ItzShubhamDev/k90r/pcb/Keyboard.kicad_sch

## KiCad design pcb/Keyboard.kicad_sch (2025-08-02)

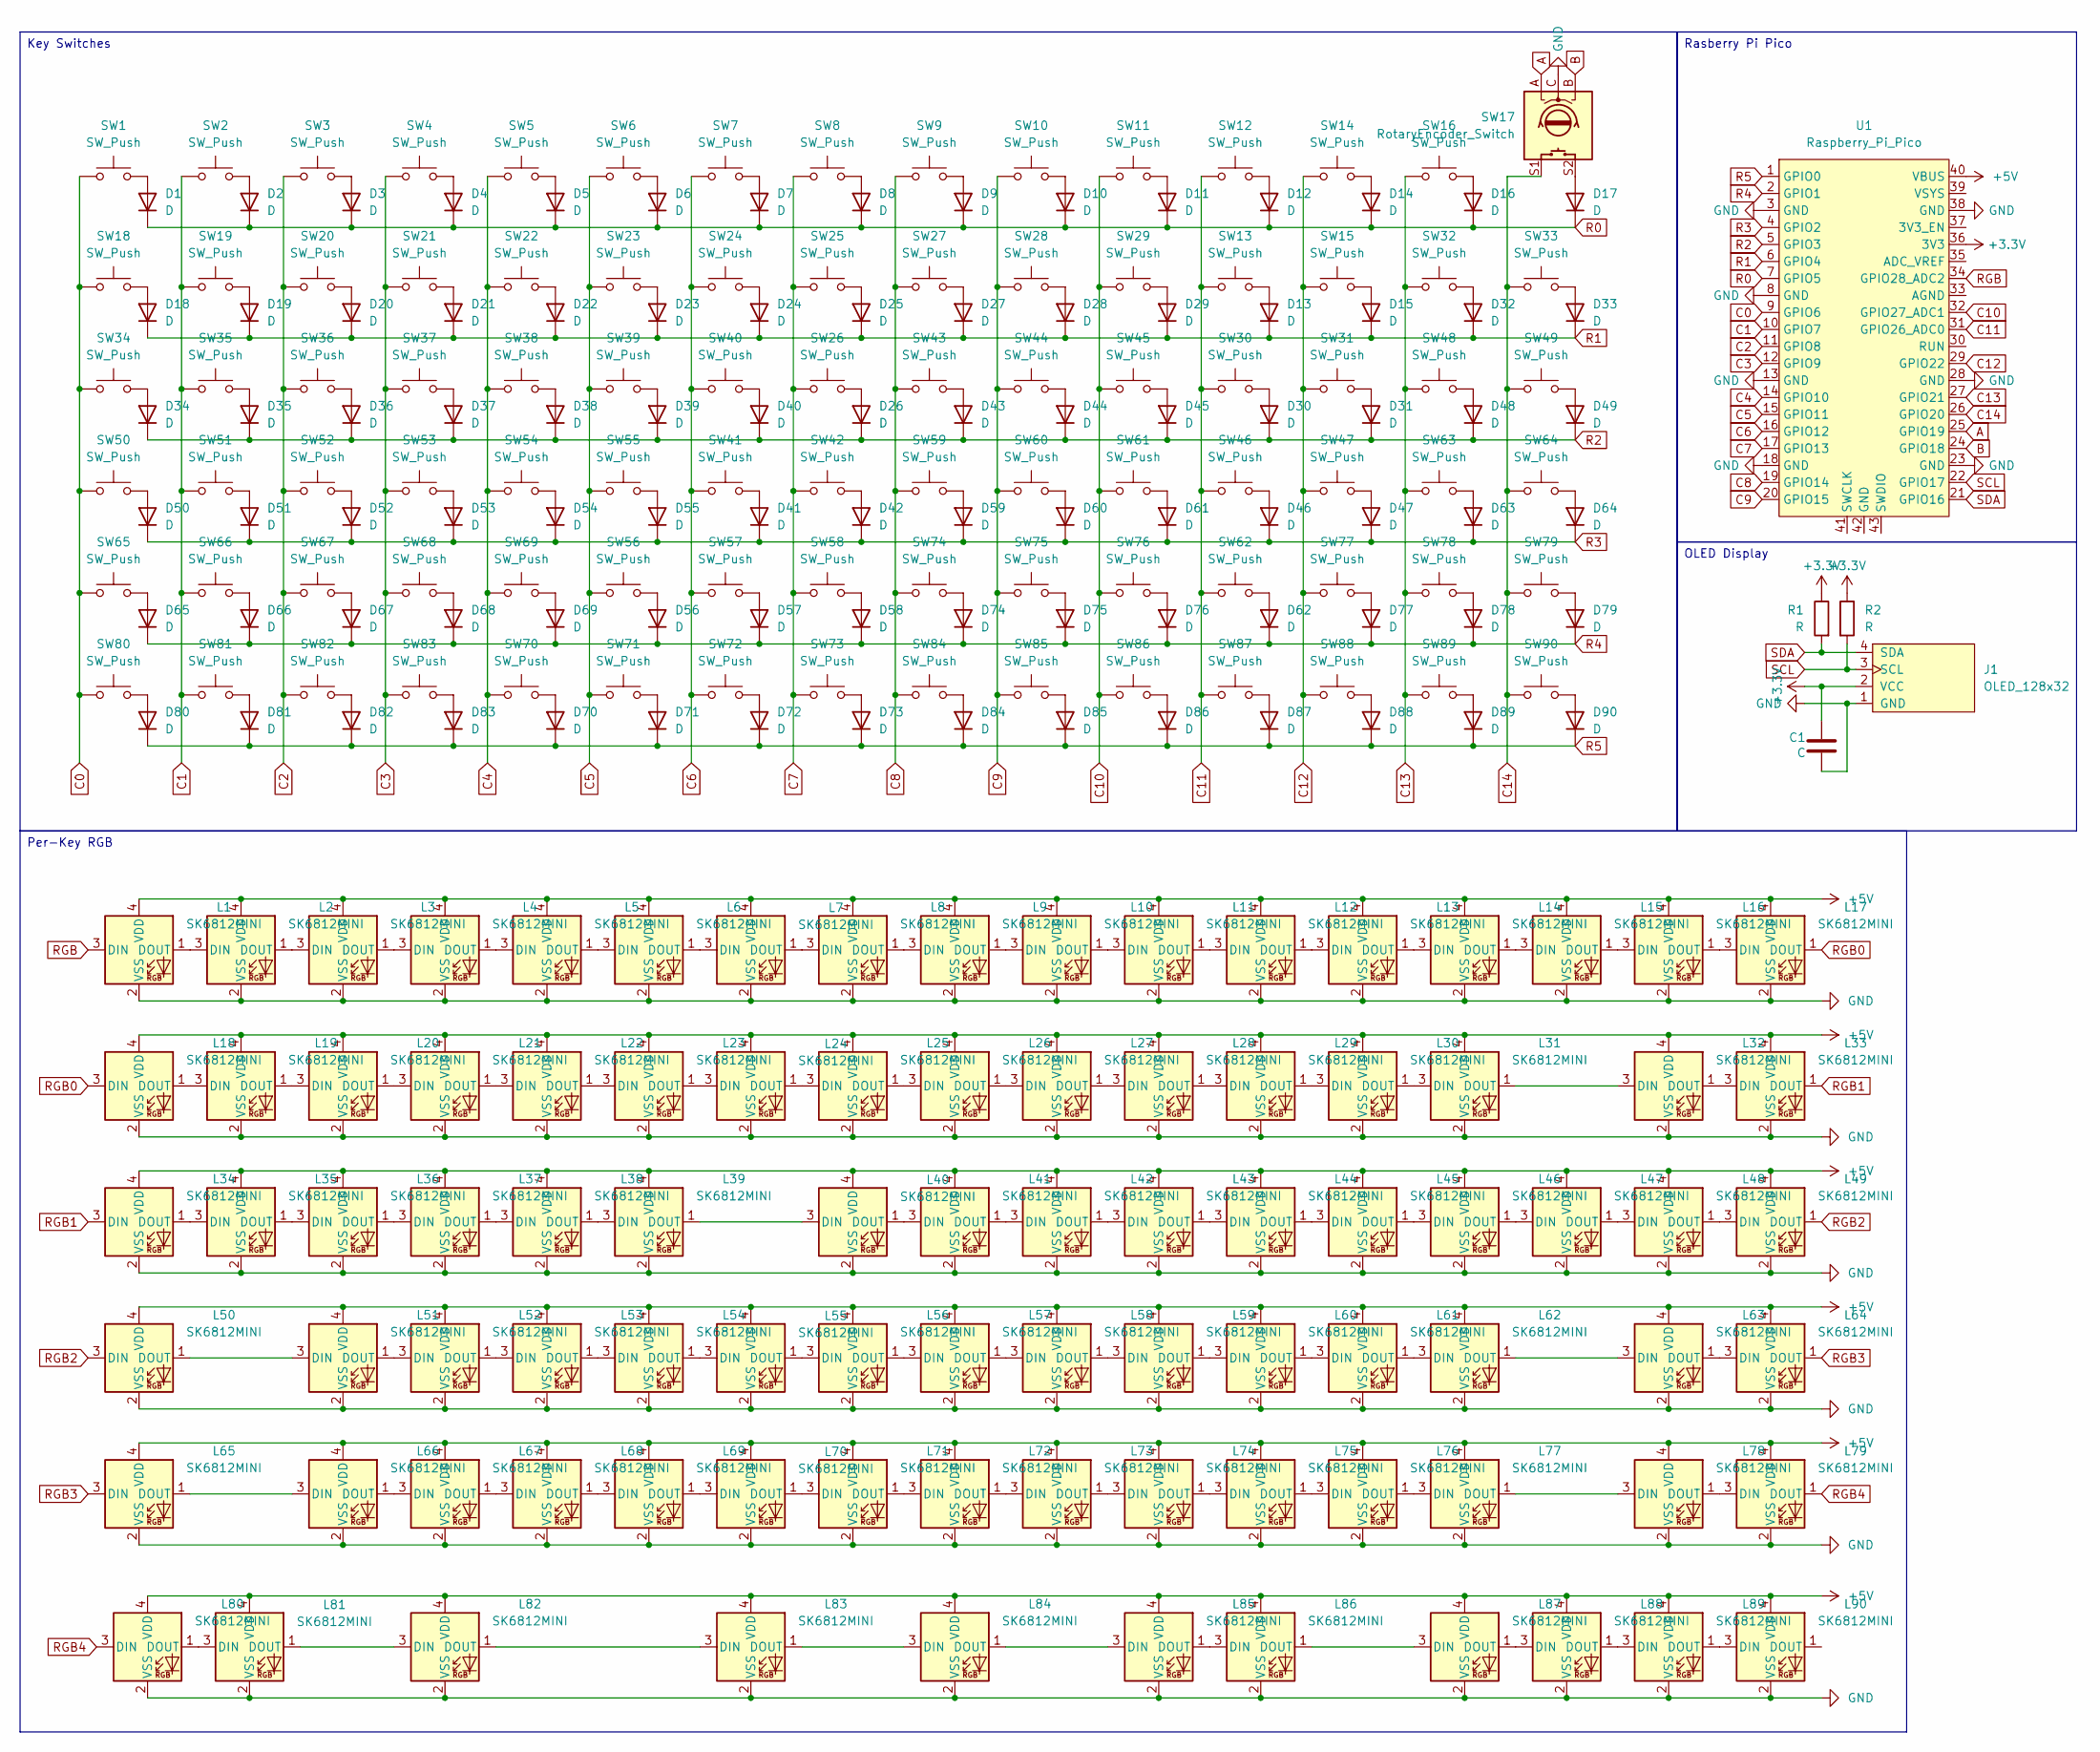
[picture p22: schematic Keyboard.kicad_sch]

Parts:
C1: C; C_Axial_L5.1mm_D3.1mm_P15.00mm_Horizontal
D1, D2, D3, D4, D5, D6, D7, D8, D9, D10, D11, D12, D13, D14, D15, D16, D17, D18, D19, D20, D21, D22, D23, D24, D25, D26, D27, D28, D29, D30, D31, D32, D33, D34, D35, D36, D37, D38, D39, D40, D41, D42, D43, D44, D45, D46, D47, D48, D49, D50, D51, D52, D53, D54, D55, D56, D57, D58, D59, D60, D61, D62, D63, D64, D65, D66, D67, D68, D69, D70, D71, D72, D73, D74, D75, D76, D77, D78, D79, D80, D81, D82, D83, D84, D85, D86, D87, D88, D89, D90: D; Diode_DO-35
J1: OLED_128x32
L1, L2, L3, L4, L5, L6, L7, L8, L9, L10, L11, L12, L13, L14, L15, L16, L17, L18, L19, L20, L21, L22, L23, L24, L25, L26, L27, L28, L29, L30, L31, L32, L33, L34, L35, L36, L37, L38, L39, L40, L41, L42, L43, L44, L45, L46, L47, L48, L49, L50, L51, L52, L53, L54, L55, L56, L57, L58, L59, L60, L61, L62, L63, L64, L65, L66, L67, L68, L69, L70, L71, L72, L73, L74, L75, L76, L77, L78, L79, L80, L81, L82, L83, L84, L85, L86, L87, L88, L89, L90: SK6812MINI; LED_SK6812MINI
R1, R2: R; R_Axial_DIN0207_L6.3mm_D2.5mm_P10.16mm_Horizontal
SW1, SW2, SW3, SW4, SW5, SW6, SW7, SW8, SW9, SW10, SW11, SW12, SW13, SW14, SW15, SW16, SW18, SW19, SW20, SW21, SW22, SW23, SW24, SW25, SW26, SW27, SW28, SW29, SW30, SW32, SW33, SW35, SW36, SW37, SW38, SW39, SW40, SW41, SW42, SW43, SW44, SW45, SW46, SW48, SW49, SW51, SW52, SW53, SW54, SW55, SW56, SW57, SW58, SW59, SW60, SW61, SW63, SW64, SW66, SW67, SW68, SW69, SW70, SW71, SW72, SW73, SW74, SW75, SW77, SW78, SW79, SW84, SW85, SW86, SW87, SW88, SW89, SW90: SW_Push; Hotswap_MX_1.00u
SW17: RotaryEncoder_Switch; Encoder_EC11_MX_Combo_1
SW31: SW_Push; Hotswap_MX_2.00u
SW34, SW47: SW_Push; Hotswap_MX_1.50u
SW50, SW76: SW_Push; Hotswap_MX_1.75u
SW62, SW65: SW_Push; Hotswap_MX_2.25u
SW80, SW81, SW82: SW_Push; Hotswap_MX_1.25u
SW83: SW_Push; Hotswap_MX_6.25u
U1: Raspberry_Pi_Pico

Connections:
+3.3V: C1.1, J1.2 (VCC), R1.1, R2.1, U1.36 (3V3)
+5V: L1.4 (VDD), L2.4 (VDD), L3.4 (VDD), L4.4 (VDD), L5.4 (VDD), L6.4 (VDD), L7.4 (VDD), L8.4 (VDD), L9.4 (VDD), L10.4 (VDD), L11.4 (VDD), L12.4 (VDD), L13.4 (VDD), L14.4 (VDD), L15.4 (VDD), L16.4 (VDD), L17.4 (VDD), L18.4 (VDD), L19.4 (VDD), L20.4 (VDD), L21.4 (VDD), L22.4 (VDD), L23.4 (VDD), L24.4 (VDD), L25.4 (VDD), L26.4 (VDD), L27.4 (VDD), L28.4 (VDD), L29.4 (VDD), L30.4 (VDD), L31.4 (VDD), L32.4 (VDD), L33.4 (VDD), L34.4 (VDD), L35.4 (VDD), L36.4 (VDD), L37.4 (VDD), L38.4 (VDD), L39.4 (VDD), L40.4 (VDD), L41.4 (VDD), L42.4 (VDD), L43.4 (VDD), L44.4 (VDD), L45.4 (VDD), L46.4 (VDD), L47.4 (VDD), L48.4 (VDD), L49.4 (VDD), L50.4 (VDD), L51.4 (VDD), L52.4 (VDD), L53.4 (VDD), L54.4 (VDD), L55.4 (VDD), L56.4 (VDD), L57.4 (VDD), L58.4 (VDD), L59.4 (VDD), L60.4 (VDD), L61.4 (VDD), L62.4 (VDD), L63.4 (VDD), L64.4 (VDD), L65.4 (VDD), L66.4 (VDD), L67.4 (VDD), L68.4 (VDD), L69.4 (VDD), L70.4 (VDD), L71.4 (VDD), L72.4 (VDD), L73.4 (VDD), L74.4 (VDD), L75.4 (VDD), L76.4 (VDD), L77.4 (VDD), L78.4 (VDD), L79.4 (VDD), L80.4 (VDD), L81.4 (VDD), L82.4 (VDD), L83.4 (VDD), L84.4 (VDD), L85.4 (VDD), L86.4 (VDD), L87.4 (VDD), L88.4 (VDD), L89.4 (VDD), L90.4 (VDD), U1.40 (VBUS)
A: SW17.A, U1.25 (GPIO19)
B: SW17.B, U1.24 (GPIO18)
C0: SW1.1, SW18.1, SW34.1, SW50.1, SW65.1, SW80.1, U1.9 (GPIO6)
C1: SW2.1, SW19.1, SW35.1, SW51.1, SW66.1, SW81.1, U1.10 (GPIO7)
C2: SW3.1, SW20.1, SW36.1, SW52.1, SW67.1, SW82.1, U1.11 (GPIO8)
C3: SW4.1, SW21.1, SW37.1, SW53.1, SW68.1, SW83.1, U1.12 (GPIO9)
C4: SW5.1, SW22.1, SW38.1, SW54.1, SW69.1, SW70.1, U1.14 (GPIO10)
C5: SW6.1, SW23.1, SW39.1, SW55.1, SW56.1, SW71.1, U1.15 (GPIO11)
C6: SW7.1, SW24.1, SW40.1, SW41.1, SW57.1, SW72.1, U1.16 (GPIO12)
C7: SW8.1, SW25.1, SW26.1, SW42.1, SW58.1, SW73.1, U1.17 (GPIO13)
C8: SW9.1, SW27.1, SW43.1, SW59.1, SW74.1, SW84.1, U1.19 (GPIO14)
C9: SW10.1, SW28.1, SW44.1, SW60.1, SW75.1, SW85.1, U1.20 (GPIO15)
C10: SW11.1, SW29.1, SW45.1, SW61.1, SW76.1, SW86.1, U1.32 (GPIO27_ADC1)
C11: SW12.1, SW13.1, SW30.1, SW46.1, SW62.1, SW87.1, U1.31 (GPIO26_ADC0)
C12: SW14.1, SW15.1, SW31.1, SW47.1, SW77.1, SW88.1, U1.29 (GPIO22)
C13: SW16.1, SW32.1, SW48.1, SW63.1, SW78.1, SW89.1, U1.27 (GPIO21)
C14: SW17.S1, SW33.1, SW49.1, SW64.1, SW79.1, SW90.1, U1.26 (GPIO20)
GND: C1.2, J1.1 (GND), L1.2 (VSS), L2.2 (VSS), L3.2 (VSS), L4.2 (VSS), L5.2 (VSS), L6.2 (VSS), L7.2 (VSS), L8.2 (VSS), L9.2 (VSS), L10.2 (VSS), L11.2 (VSS), L12.2 (VSS), L13.2 (VSS), L14.2 (VSS), L15.2 (VSS), L16.2 (VSS), L17.2 (VSS), L18.2 (VSS), L19.2 (VSS), L20.2 (VSS), L21.2 (VSS), L22.2 (VSS), L23.2 (VSS), L24.2 (VSS), L25.2 (VSS), L26.2 (VSS), L27.2 (VSS), L28.2 (VSS), L29.2 (VSS), L30.2 (VSS), L31.2 (VSS), L32.2 (VSS), L33.2 (VSS), L34.2 (VSS), L35.2 (VSS), L36.2 (VSS), L37.2 (VSS), L38.2 (VSS), L39.2 (VSS), L40.2 (VSS), L41.2 (VSS), L42.2 (VSS), L43.2 (VSS), L44.2 (VSS), L45.2 (VSS), L46.2 (VSS), L47.2 (VSS), L48.2 (VSS), L49.2 (VSS), L50.2 (VSS), L51.2 (VSS), L52.2 (VSS), L53.2 (VSS), L54.2 (VSS), L55.2 (VSS), L56.2 (VSS), L57.2 (VSS), L58.2 (VSS), L59.2 (VSS), L60.2 (VSS), L61.2 (VSS), L62.2 (VSS), L63.2 (VSS), L64.2 (VSS), L65.2 (VSS), L66.2 (VSS), L67.2 (VSS), L68.2 (VSS), L69.2 (VSS), L70.2 (VSS), L71.2 (VSS), L72.2 (VSS), L73.2 (VSS), L74.2 (VSS), L75.2 (VSS), L76.2 (VSS), L77.2 (VSS), L78.2 (VSS), L79.2 (VSS), L80.2 (VSS), L81.2 (VSS), L82.2 (VSS), L83.2 (VSS), L84.2 (VSS), L85.2 (VSS), L86.2 (VSS), L87.2 (VSS), L88.2 (VSS), L89.2 (VSS), L90.2 (VSS), SW17.C, U1.3 (GND), U1.8 (GND), U1.13 (GND), U1.18 (GND), U1.23 (GND), U1.28 (GND), U1.38 (GND)
unnamed: D1.2 (A), SW1.2
unnamed: D2.2 (A), SW2.2
unnamed: D3.2 (A), SW3.2
unnamed: D4.2 (A), SW4.2
unnamed: D5.2 (A), SW5.2
unnamed: D6.2 (A), SW6.2
unnamed: D7.2 (A), SW7.2
unnamed: D8.2 (A), SW8.2
unnamed: D9.2 (A), SW9.2
unnamed: D10.2 (A), SW10.2
unnamed: D11.2 (A), SW11.2
unnamed: D12.2 (A), SW12.2
unnamed: D13.2 (A), SW13.2
unnamed: D14.2 (A), SW14.2
unnamed: D15.2 (A), SW15.2
unnamed: D16.2 (A), SW16.2
unnamed: D17.2 (A), SW17.S2
unnamed: D18.2 (A), SW18.2
unnamed: D19.2 (A), SW19.2
unnamed: D20.2 (A), SW20.2
unnamed: D21.2 (A), SW21.2
unnamed: D22.2 (A), SW22.2
unnamed: D23.2 (A), SW23.2
unnamed: D24.2 (A), SW24.2
unnamed: D25.2 (A), SW25.2
unnamed: D26.2 (A), SW26.2
unnamed: D27.2 (A), SW27.2
unnamed: D28.2 (A), SW28.2
unnamed: D29.2 (A), SW29.2
unnamed: D30.2 (A), SW30.2
unnamed: D31.2 (A), SW31.2
unnamed: D32.2 (A), SW32.2
unnamed: D33.2 (A), SW33.2
unnamed: D34.2 (A), SW34.2
unnamed: D35.2 (A), SW35.2
unnamed: D36.2 (A), SW36.2
unnamed: D37.2 (A), SW37.2
unnamed: D38.2 (A), SW38.2
unnamed: D39.2 (A), SW39.2
unnamed: D40.2 (A), SW40.2
unnamed: D41.2 (A), SW41.2
unnamed: D42.2 (A), SW42.2
unnamed: D43.2 (A), SW43.2
unnamed: D44.2 (A), SW44.2
unnamed: D45.2 (A), SW45.2
unnamed: D46.2 (A), SW46.2
unnamed: D47.2 (A), SW47.2
unnamed: D48.2 (A), SW48.2
unnamed: D49.2 (A), SW49.2
unnamed: D50.2 (A), SW50.2
unnamed: D51.2 (A), SW51.2
unnamed: D52.2 (A), SW52.2
unnamed: D53.2 (A), SW53.2
unnamed: D54.2 (A), SW54.2
unnamed: D55.2 (A), SW55.2
unnamed: D56.2 (A), SW56.2
unnamed: D57.2 (A), SW57.2
unnamed: D58.2 (A), SW58.2
unnamed: D59.2 (A), SW59.2
unnamed: D60.2 (A), SW60.2
unnamed: D61.2 (A), SW61.2
unnamed: D62.2 (A), SW62.2
unnamed: D63.2 (A), SW63.2
unnamed: D64.2 (A), SW64.2
unnamed: D65.2 (A), SW65.2
unnamed: D66.2 (A), SW66.2
unnamed: D67.2 (A), SW67.2
unnamed: D68.2 (A), SW68.2
unnamed: D69.2 (A), SW69.2
unnamed: D70.2 (A), SW70.2
unnamed: D71.2 (A), SW71.2
unnamed: D72.2 (A), SW72.2
unnamed: D73.2 (A), SW73.2
unnamed: D74.2 (A), SW74.2
unnamed: D75.2 (A), SW75.2
unnamed: D76.2 (A), SW76.2
unnamed: D77.2 (A), SW77.2
unnamed: D78.2 (A), SW78.2
unnamed: D79.2 (A), SW79.2
unnamed: D80.2 (A), SW80.2
unnamed: D81.2 (A), SW81.2
unnamed: D82.2 (A), SW82.2
unnamed: D83.2 (A), SW83.2
unnamed: D84.2 (A), SW84.2
unnamed: D85.2 (A), SW85.2
unnamed: D86.2 (A), SW86.2
unnamed: D87.2 (A), SW87.2
unnamed: D88.2 (A), SW88.2
unnamed: D89.2 (A), SW89.2
unnamed: D90.2 (A), SW90.2
unnamed: L1.1 (DOUT), L2.3 (DIN)
unnamed: L2.1 (DOUT), L3.3 (DIN)
unnamed: L3.1 (DOUT), L4.3 (DIN)
unnamed: L4.1 (DOUT), L5.3 (DIN)
unnamed: L5.1 (DOUT), L6.3 (DIN)
unnamed: L6.1 (DOUT), L7.3 (DIN)
unnamed: L7.1 (DOUT), L8.3 (DIN)
unnamed: L8.1 (DOUT), L9.3 (DIN)
unnamed: L10.1 (DOUT), L11.3 (DIN)
unnamed: L9.1 (DOUT), L10.3 (DIN)
unnamed: L11.1 (DOUT), L12.3 (DIN)
unnamed: L12.1 (DOUT), L13.3 (DIN)
unnamed: L13.1 (DOUT), L14.3 (DIN)
unnamed: L14.1 (DOUT), L15.3 (DIN)
unnamed: L15.1 (DOUT), L16.3 (DIN)
unnamed: L16.1 (DOUT), L17.3 (DIN)
unnamed: L18.1 (DOUT), L19.3 (DIN)
unnamed: L19.1 (DOUT), L20.3 (DIN)
unnamed: L20.1 (DOUT), L21.3 (DIN)
unnamed: L21.1 (DOUT), L22.3 (DIN)
unnamed: L22.1 (DOUT), L23.3 (DIN)
unnamed: L23.1 (DOUT), L24.3 (DIN)
unnamed: L24.1 (DOUT), L25.3 (DIN)
unnamed: L25.1 (DOUT), L26.3 (DIN)
unnamed: L26.1 (DOUT), L27.3 (DIN)
unnamed: L27.1 (DOUT), L28.3 (DIN)
unnamed: L28.1 (DOUT), L29.3 (DIN)
unnamed: L29.1 (DOUT), L30.3 (DIN)
unnamed: L30.1 (DOUT), L31.3 (DIN)
unnamed: L31.1 (DOUT), L32.3 (DIN)
unnamed: L32.1 (DOUT), L33.3 (DIN)
unnamed: L34.1 (DOUT), L35.3 (DIN)
unnamed: L35.1 (DOUT), L36.3 (DIN)
unnamed: L36.1 (DOUT), L37.3 (DIN)
unnamed: L37.1 (DOUT), L38.3 (DIN)
unnamed: L38.1 (DOUT), L39.3 (DIN)
unnamed: L39.1 (DOUT), L40.3 (DIN)
unnamed: L40.1 (DOUT), L41.3 (DIN)
unnamed: L41.1 (DOUT), L42.3 (DIN)
unnamed: L42.1 (DOUT), L43.3 (DIN)
unnamed: L43.1 (DOUT), L44.3 (DIN)
unnamed: L44.1 (DOUT), L45.3 (DIN)
unnamed: L45.1 (DOUT), L46.3 (DIN)
unnamed: L46.1 (DOUT), L47.3 (DIN)
unnamed: L47.1 (DOUT), L48.3 (DIN)
unnamed: L48.1 (DOUT), L49.3 (DIN)
unnamed: L50.1 (DOUT), L51.3 (DIN)
unnamed: L51.1 (DOUT), L52.3 (DIN)
unnamed: L52.1 (DOUT), L53.3 (DIN)
unnamed: L53.1 (DOUT), L54.3 (DIN)
unnamed: L54.1 (DOUT), L55.3 (DIN)
unnamed: L55.1 (DOUT), L56.3 (DIN)
unnamed: L56.1 (DOUT), L57.3 (DIN)
unnamed: L57.1 (DOUT), L58.3 (DIN)
unnamed: L58.1 (DOUT), L59.3 (DIN)
unnamed: L59.1 (DOUT), L60.3 (DIN)
unnamed: L60.1 (DOUT), L61.3 (DIN)
unnamed: L61.1 (DOUT), L62.3 (DIN)
unnamed: L62.1 (DOUT), L63.3 (DIN)
unnamed: L63.1 (DOUT), L64.3 (DIN)
unnamed: L65.1 (DOUT), L66.3 (DIN)
unnamed: L66.1 (DOUT), L67.3 (DIN)
unnamed: L67.1 (DOUT), L68.3 (DIN)
unnamed: L68.1 (DOUT), L69.3 (DIN)
unnamed: L69.1 (DOUT), L70.3 (DIN)
unnamed: L70.1 (DOUT), L71.3 (DIN)
unnamed: L71.1 (DOUT), L72.3 (DIN)
unnamed: L72.1 (DOUT), L73.3 (DIN)
unnamed: L73.1 (DOUT), L74.3 (DIN)
unnamed: L74.1 (DOUT), L75.3 (DIN)
unnamed: L75.1 (DOUT), L76.3 (DIN)
unnamed: L76.1 (DOUT), L77.3 (DIN)
unnamed: L77.1 (DOUT), L78.3 (DIN)
unnamed: L78.1 (DOUT), L79.3 (DIN)
unnamed: L80.1 (DOUT), L81.3 (DIN)
unnamed: L81.1 (DOUT), L82.3 (DIN)
unnamed: L82.1 (DOUT), L83.3 (DIN)
unnamed: L83.1 (DOUT), L84.3 (DIN)
unnamed: L84.1 (DOUT), L85.3 (DIN)
unnamed: L85.1 (DOUT), L86.3 (DIN)
unnamed: L86.1 (DOUT), L87.3 (DIN)
unnamed: L87.1 (DOUT), L88.3 (DIN)
unnamed: L88.1 (DOUT), L89.3 (DIN)
unnamed: L89.1 (DOUT), L90.3 (DIN)
R0: D1.1 (K), D2.1 (K), D3.1 (K), D4.1 (K), D5.1 (K), D6.1 (K), D7.1 (K), D8.1 (K), D9.1 (K), D10.1 (K), D11.1 (K), D12.1 (K), D14.1 (K), D16.1 (K), D17.1 (K), U1.7 (GPIO5)
R1: D13.1 (K), D15.1 (K), D18.1 (K), D19.1 (K), D20.1 (K), D21.1 (K), D22.1 (K), D23.1 (K), D24.1 (K), D25.1 (K), D27.1 (K), D28.1 (K), D29.1 (K), D32.1 (K), D33.1 (K), U1.6 (GPIO4)
R2: D26.1 (K), D30.1 (K), D31.1 (K), D34.1 (K), D35.1 (K), D36.1 (K), D37.1 (K), D38.1 (K), D39.1 (K), D40.1 (K), D43.1 (K), D44.1 (K), D45.1 (K), D48.1 (K), D49.1 (K), U1.5 (GPIO3)
R3: D41.1 (K), D42.1 (K), D46.1 (K), D47.1 (K), D50.1 (K), D51.1 (K), D52.1 (K), D53.1 (K), D54.1 (K), D55.1 (K), D59.1 (K), D60.1 (K), D61.1 (K), D63.1 (K), D64.1 (K), U1.4 (GPIO2)
R4: D56.1 (K), D57.1 (K), D58.1 (K), D62.1 (K), D65.1 (K), D66.1 (K), D67.1 (K), D68.1 (K), D69.1 (K), D74.1 (K), D75.1 (K), D76.1 (K), D77.1 (K), D78.1 (K), D79.1 (K), U1.2 (GPIO1)
R5: D70.1 (K), D71.1 (K), D72.1 (K), D73.1 (K), D80.1 (K), D81.1 (K), D82.1 (K), D83.1 (K), D84.1 (K), D85.1 (K), D86.1 (K), D87.1 (K), D88.1 (K), D89.1 (K), D90.1 (K), U1.1 (GPIO0)
RGB: L1.3 (DIN), U1.34 (GPIO28_ADC2)
RGB0: L17.1 (DOUT), L18.3 (DIN)
RGB1: L33.1 (DOUT), L34.3 (DIN)
RGB2: L49.1 (DOUT), L50.3 (DIN)
RGB3: L64.1 (DOUT), L65.3 (DIN)
RGB4: L79.1 (DOUT), L80.3 (DIN)
SCL: J1.3 (SCL), R2.2, U1.22 (GPIO17)
SDA: J1.4 (SDA), R1.2, U1.21 (GPIO16)

Notes on the sheet:
OLED Display
Key Switches
Per-Key RGB
Rasberry Pi Pico
